DeuxVis/HaveSome_PCB/Doc/V1.0_OSHPark-left_PCBs.io-right.jpg

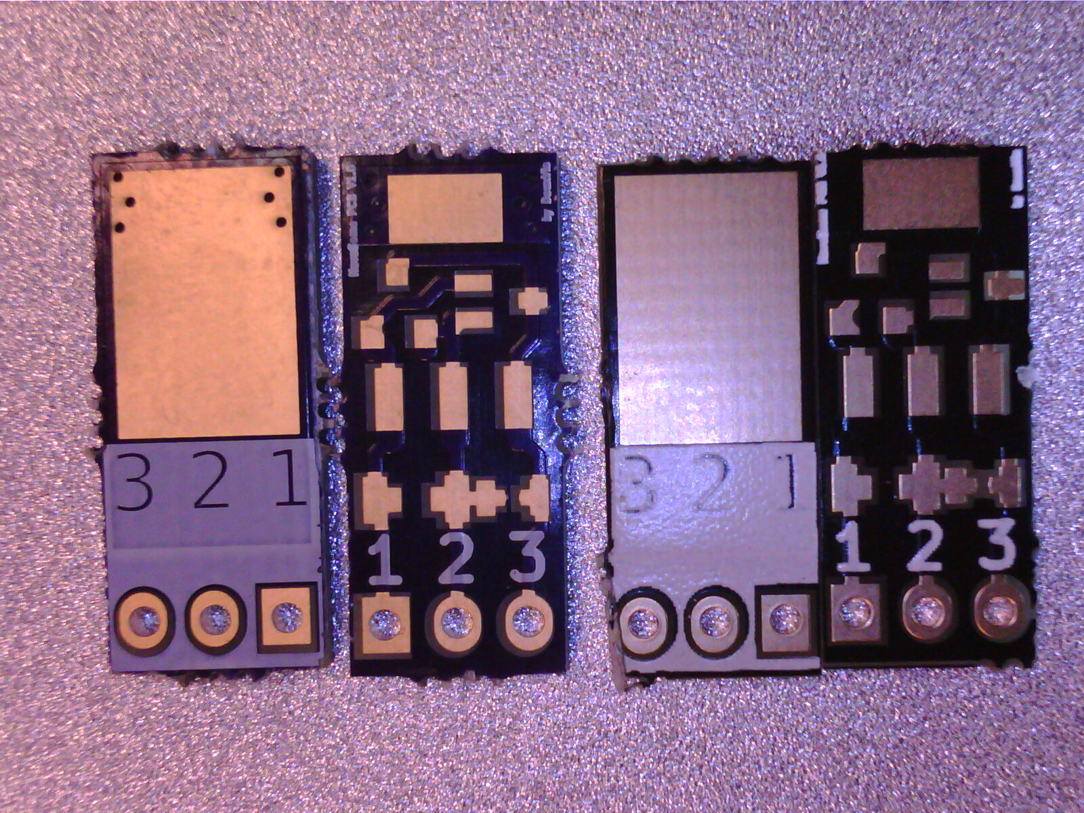
Doc/V1.0_OSHPark-left_PCBs.io-right.jpg
