DeuxVis/HaveSome_PCB/HaveSomePCB_kicad/notezone.png

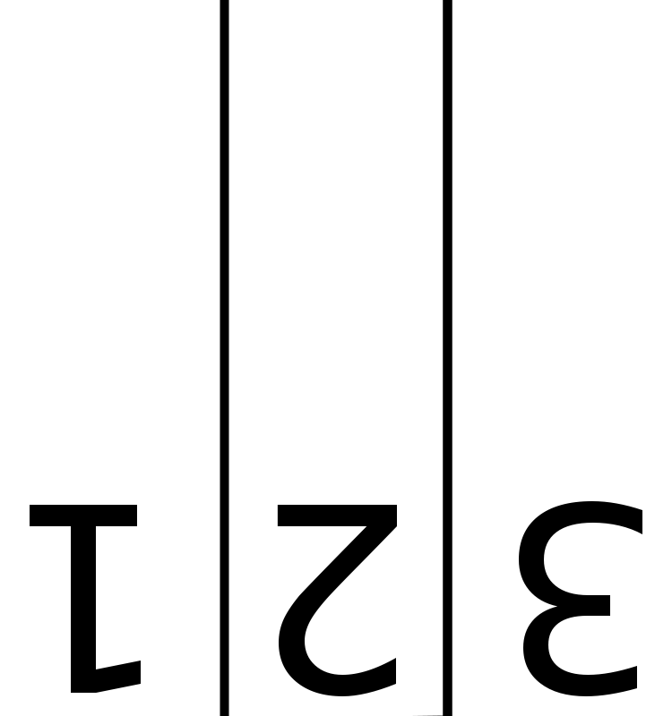
HaveSomePCB_kicad/notezone.png
